AFNordal/ntnu-nyhavna-s24/tracking-box/firmware/src/bmi270.cpp

#include "bmi270.h"

void bmi_init(const uint8_t sda_pin, const uint8_t scl_pin)
{
    i2c_init(BMI_I2C, 1000 * 1000);
    gpio_set_function(sda_pin, GPIO_FUNC_I2C);
    gpio_set_function(scl_pin, GPIO_FUNC_I2C);
    gpio_pull_up(sda_pin);
    gpio_pull_up(scl_pin);

    // Reset all registers
    busy_wait_cycles_ms(10);
    bmi_softreset();
    busy_wait_cycles_ms(10);

    bmi_write(BMI_PWR_CONF_R, (0x00 << 0) | (0x01 << 1));

    // Load config file
    bmi_write(BMI_INIT_CTRL_R, 0x00);
    bmi_write_arr(BMI_INIT_DATA_R, sizeof(bmi270_config_file), bmi270_config_file);
    bmi_write(BMI_INIT_CTRL_R, 0x01);
    busy_wait_cycles_ms(20);


    uint8_t init_status = bmi_read(BMI_INTERNAL_STATUS_R);
    if ((init_status & 0x0F) != 0x1)
        FATAL("BMI270 initialization failed with error code 0x%x\n", init_status);
    // Acc: 1.6KHz ODR, normal filtering
    bmi_write(BMI_ACC_CONF_R, (0x0c << 0) | (0x02 << 4) | (0x01 << 7));
    // Gyro: 1.6KHz ODR, normal filtering, low-noise
    bmi_write(BMI_GYR_CONF_R, (0x0c << 0) | (0x02 << 4) | (0x01 << 6) | (0x01 << 7));
    // Acc: +/- 2g
    bmi_write(BMI_ACC_RANGE_R, 0x00);
    // Gyro: +/-250 dps, 131.2 LSB/dps
    bmi_write(BMI_GYR_RANGE_R, (0x03 << 0) | (0x01 << 3));

    // Gyro downsample by 4 to get 1.6KHz, unifltered data, no acc downsample
    bmi_write(BMI_FIFO_DOWNS_R, (0x02 << 0) | (0x00 << 3) | (0x00 << 4) | (0x00 << 7));
    // FIFO watermark 6 bytes
    bmi_write(BMI_FIFO_WTM_0_R, 0x06);
    bmi_write(BMI_FIFO_WTM_1_R, 0x00);

    // Map watermark to INT1
    bmi_write(BMI_INT_MAP_DATA_R, (0x01 << 1));
    // Enable INT1 output, active high
    bmi_write(BMI_INT1_IO_CTRL_R, (0x01 << 1) | (0x01 << 3));

    // Disable sensortime frames
    bmi_write(BMI_FIFO_CONFIG_0_R, (0x00 << 1));
    // Headerless FIFO, enable acc and gyr data to FIFO
    bmi_write(BMI_FIFO_CONFIG_1_R, (0x00 << 4) | (0x01 << 6) | (0x01 << 7));

    bmi_check_error();

    // Enable gyro and acc
    bmi_write(BMI_PWR_CTRL_R, (0x01 << 1) | (0x01 << 2));
    // info_blink();
}

void bmi_print_status(void)
{
    uint8_t statusdata = bmi_read(BMI_STATUS_R);
    INFO("%x\n", statusdata);
}

void bmi_read_arr(uint8_t addr, size_t len, uint8_t *rxdata)
{
    i2c_write_blocking(BMI_I2C, BMI_I2C_ADDR, &addr, 1, false);
    size_t bytes_read = i2c_read_blocking(BMI_I2C, BMI_I2C_ADDR, rxdata, len, false);
    if (bytes_read != len)
    {
        WARNING("BMI read error: Read %d/%d bytes\n", bytes_read, len);
    }
}

void bmi_write_arr(uint8_t addr, size_t len, const uint8_t *txdata)
{
    uint8_t txarr[len + 1];
    txarr[0] = addr;
    memcpy(txarr + 1, txdata, len);
    size_t bytes_written = i2c_write_blocking(BMI_I2C, BMI_I2C_ADDR, txarr, len + 1, false);
    if (bytes_written != len + 1)
    {
        WARNING("BMI write error: Read %d/%d bytes\n", bytes_written, len + 1);
    }
    busy_wait_cycles_us(450);
}

void bmi_write(uint8_t addr, uint8_t txdata)
{
    uint8_t txarr[] = {addr, txdata};
    size_t bytes_written = i2c_write_blocking(BMI_I2C, BMI_I2C_ADDR, txarr, 2, false);
    if (bytes_written != 2)
    {
        WARNING("BMI write error\n");
    }
    busy_wait_cycles_us(450);
}

uint8_t bmi_read(uint8_t addr)
{
    uint8_t rxdata;
    i2c_write_blocking(BMI_I2C, BMI_I2C_ADDR, &addr, 1, false);
    if (i2c_read_blocking(BMI_I2C, BMI_I2C_ADDR, &rxdata, 1, false) != 1)
    {
        WARNING("BMI read error\n");
        return -1;
    }
    else
    {
        return rxdata;
    }
}

void bmi_check_error(void)
{
    uint8_t errordata = bmi_read(BMI_INTERNAL_ERROR_R);
    if ((errordata & (1 << 2)) != 0)
    {
        FATAL("Internal bmi error: Fatal\n");
    }
    else if ((errordata & (1 << 1)) != 0)
    {
        ERROR("Internal bmi error: Long processing time\n");
    }
}

void bmi_flush_FIFO(void)
{
    bmi_write(BMI_CMD_R, 0xb0);
}

void bmi_softreset(void)
{
    bmi_write(BMI_CMD_R, 0xb6);
}

void bmi_read_FIFO(uint8_t *rxdata, uint16_t len)
{
    bmi_read_arr(BMI_FIFO_DATA_R, len, rxdata);
}

// Checks if watermark interrupt is triggered
bool bmi_drdy(void)
{
    uint8_t intstatus = bmi_read(BMI_INT_STATUS_1_R);
    return bool(intstatus);
}

uint16_t bmi_get_FIFO_length(void)
{
    uint16_t len;
    bmi_read_arr(BMI_FIFO_LENGTH_0_R, 2, (uint8_t *)&len);
    return len;
}

uint8_t bmi_read_sensors(bmi_data_t *data)
{
    uint16_t len = bmi_get_FIFO_length();
    if (len == 0)
    {
        return 1;
    }
    ASSERT(len <= 12);
    uint8_t rxdata[len];
    bmi_read_FIFO(rxdata, len);
    data->gx = (int16_t)((rxdata[1] << 8) | rxdata[0]);
    data->gy = (int16_t)((rxdata[3] << 8) | rxdata[2]);
    data->gz = (int16_t)((rxdata[5] << 8) | rxdata[4]);
    data->ax = (int16_t)((rxdata[7] << 8) | rxdata[6]);
    data->ay = (int16_t)((rxdata[9] << 8) | rxdata[8]);
    data->az = (int16_t)((rxdata[11] << 8) | rxdata[10]);
    return 0;
}

void print_bmi_data(bmi_data_t *data)
{
    printf("gx:%d,", data->gx);
    printf("gy:%d,", data->gy);
    printf("gz:%d,", data->gz);
    printf("ax:%d,", data->ax);
    printf("ay:%d,", data->ay);
    printf("az:%d\n", data->az);
}

void bmi_set_drdy_pin(const uint8_t pin, void (*callback)(uint gpio, uint32_t event_mask))
{
    gpio_set_irq_enabled_with_callback(pin, GPIO_IRQ_EDGE_RISE, true, callback);
}
