AFNordal/ntnu-nyhavna-s24/tracking-box/firmware/src/hw_config.cpp

/* hw_config.c
Copyright 2021 Carl John Kugler III

Licensed under the Apache License, Version 2.0 (the License); you may not use
this file except in compliance with the License. You may obtain a copy of the
License at

   http://www.apache.org/licenses/LICENSE-2.0
Unless required by applicable law or agreed to in writing, software distributed
under the License is distributed on an AS IS BASIS, WITHOUT WARRANTIES OR
CONDITIONS OF ANY KIND, either express or implied. See the License for the
specific language governing permissions and limitations under the License.
*/
/*   
This file should be tailored to match the hardware design.

See 
https://github.com/carlk3/no-OS-FatFS-SD-SDIO-SPI-RPi-Pico/tree/main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
*/

#include "hw_config.h"

/* Configuration of RP2040 hardware SPI object */
static spi_t spi = {  
    .hw_inst = spi0,  // RP2040 SPI component
    .miso_gpio = 16,
    .mosi_gpio = 19,
    .sck_gpio = 18,    // GPIO number (not Pico pin number)
    .baud_rate = 25 * 1000 * 1000,
    .DMA_IRQ_num = DMA_IRQ_0,
    .use_exclusive_DMA_IRQ_handler = true,
    .use_static_dma_channels = false
};

/* SPI Interface */
static sd_spi_if_t spi_if = {
    .spi = &spi,  // Pointer to the SPI driving this card
    .ss_gpio = 17      // The SPI slave select GPIO for this SD card
};

/* Configuration of the SD Card socket object */
static sd_card_t sd_card = {   
    .type = SD_IF_SPI,
    .spi_if_p = &spi_if  // Pointer to the SPI interface driving this card
};

/* ********************************************************************** */

size_t sd_get_num() { return 1; }

sd_card_t *sd_get_by_num(size_t num) {
    if (0 == num) {
        return &sd_card;
    } else {
        return NULL;
    }
}

/* [] END OF FILE */
